tamaygz/esp-wled-projects/reefs/mechanical/enclosure/reefs-automatedvariant-base-top.png

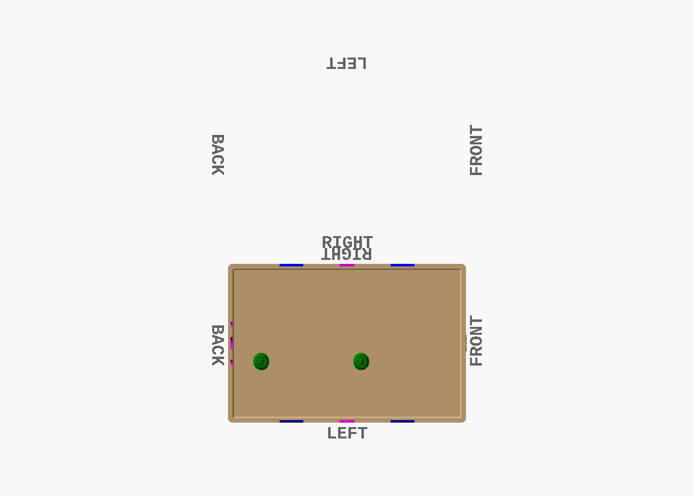
reefs/mechanical/enclosure/reefs-automatedvariant-base-top.png
